bathiy/Analog-Inductance-and-Capacitance-Measuring-Meter/Inductance measuring circuit/circuit_design/Draft1.asc

C1: cap; 10µF
C2: cap; 40nF
C3: cap; 22nF
C4: cap; 22nF
C5: cap; 40nF
C6: cap; 22p
C8: cap; 50µ
C9: cap; 100n
D1: diode; 1N4148
D2: diode; 1N4148
L1: ind; 1mH
L2: ind; 1m
Q1: npn; 2N2222
R1: res; 12k
R2: res; 8.2k
R3: res; 1k
R4: res; 1k
R5: res; 100
R6: res; 1k
R7: res; 1k
R8: res; 1k
R9: res; 15k
U1: OP07
V1: voltage; 9V
V2: voltage; 15
V3: voltage; 15
Named nets: 0
.tran 0 0.5 0
Variable Inductor
