bathiy/Analog-Inductance-and-Capacitance-Measuring-Meter/Inductance measuring circuit/circuit_design/Draft2.asc

C1: cap; 1µ
R1: res; 150k
R2: res; 60k
R3: res; 43k
U1: OP07
V1: voltage; 15
V2: voltage; 15
Named nets: 0
.tran 0 1 0
