bathiy/Analog-Inductance-and-Capacitance-Measuring-Meter/Inductance measuring circuit/circuit_design/LM2917-14 test.asc

C1: cap; 10nF
C2: cap; .1µF
C3: cap; .1µF
C4: cap; 10µF
C5: cap; .1µF
R1: res; 47k
R2: res; 9.1k
R3: res; 1k
R4: res; 47k
R5: res; 10k
R6: res; 100k
Rzener: res; 470
U1: LM2917-14
V1: voltage; 14; Rser=0.3
V2: voltage; SINE(0 .1 200k)
Named nets: 0, Vcc, +in, c1ext, c2ext, Out, -in, Out2
.tran 0 100m 0 10u startup
