bathiy/Analog-Inductance-and-Capacitance-Measuring-Meter/Inductance measuring circuit/circuit_design/Nisal-INVENSION.asc

C1: cap; 22p
C2: cap; 50µ
C3: cap; 100n
D1: diode; 1N4148
D2: diode; 1N4148
L1: ind; 1m
R1: res; 1k
R2: res; 1k
R3: res; 1k
R4: res; 15k
U1: UniversalOpAmp1
V1: voltage; SINE(0 5 35k); AC 1
V2: voltage; 15
V3: voltage; 15
Named nets: 0
.ac oct 1 20k 400k
