bathiy/Analog-Inductance-and-Capacitance-Measuring-Meter/Capacitor measuring circuit/circuit_design/cap.asc

C1: cap; 15n
D1: diode
R1: res; 150k
R2: res; 60k
R3: res; 43k
R4: res; 10k
R5: res; 25k
R6: res; 5k
U1: OP07
U2: OP07
V1: voltage; 15
V2: voltage; 15
Named nets: 0
.tran 0 1 0
